thetheos/StrainGauge/photos/IMG_20170623_125859.jpg

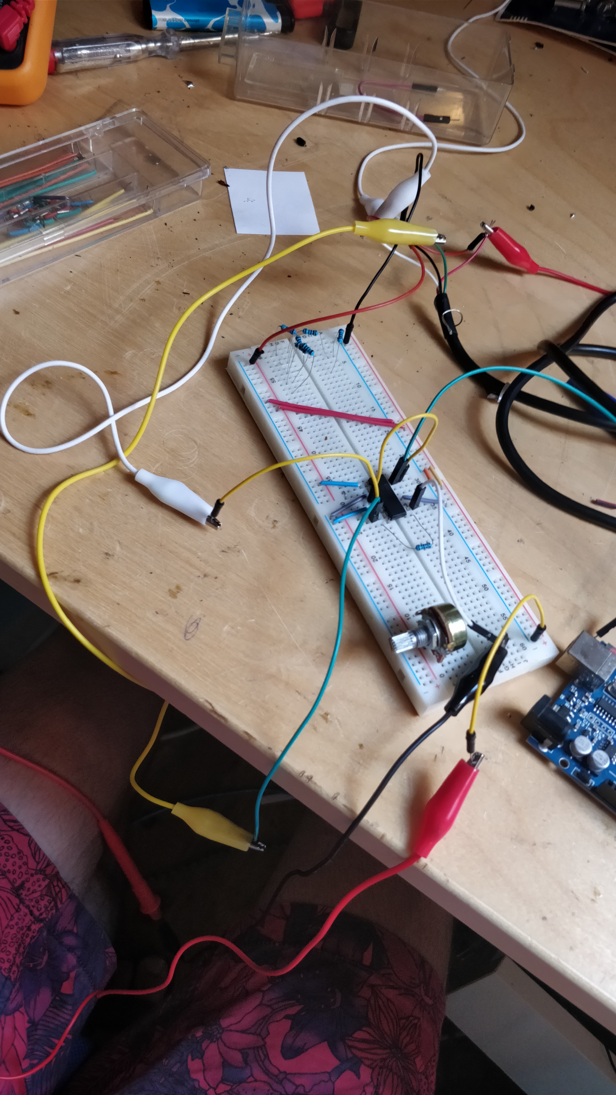
photos/IMG_20170623_125859.jpg
