thetheos/StrainGauge/photos/IMG_20170623_130728.jpg

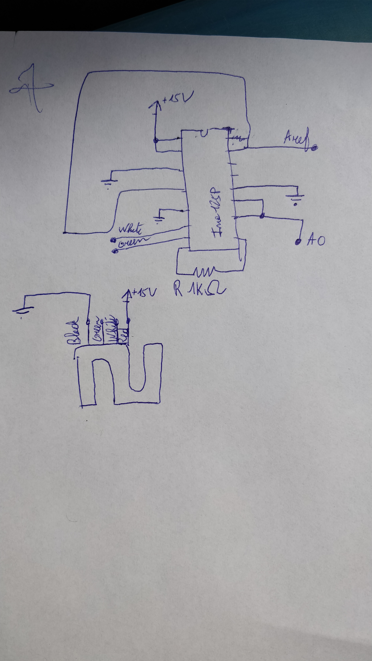
photos/IMG_20170623_130728.jpg
