thetheos/StrainGauge/photos/IMG_20170704_001040.jpg

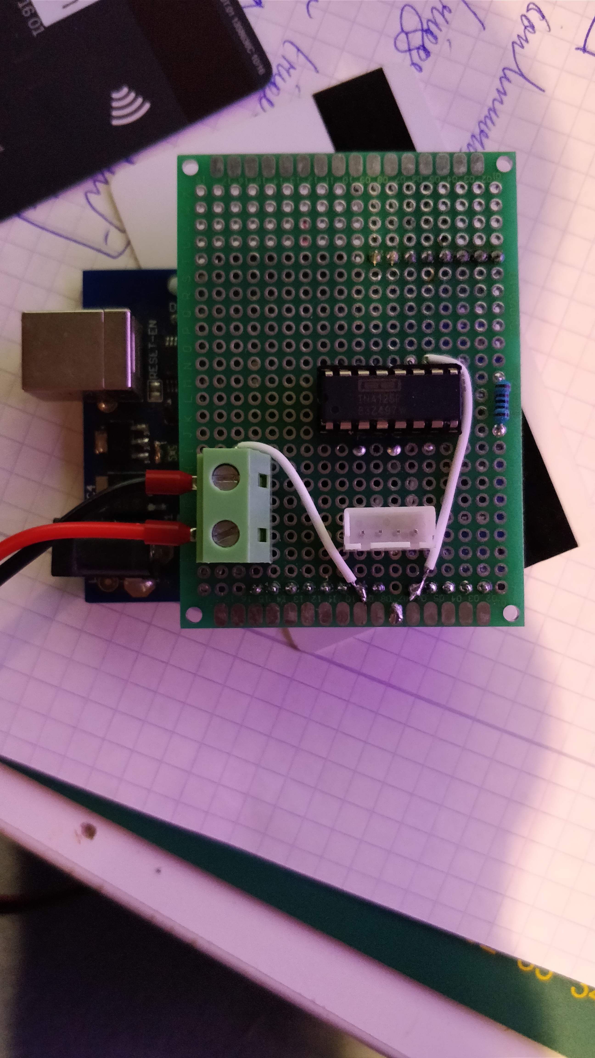
photos/IMG_20170704_001040.jpg
