thetheos/StrainGauge/test python/encoder.h

/* Encoder Library, for measuring quadrature encoded signals
 * http://www.pjrc.com/teensy/td_libs_Encoder.html
 * Copyright (c) 2011,2013 PJRC.COM, LLC - Paul Stoffregen <paul@pjrc.com>
 *
 * Version 1.2 - fix -2 bug in C-only code
 * Version 1.1 - expand to support boards with up to 60 interrupts
 * Version 1.0 - initial release
 * 
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
 * THE SOFTWARE IS PROVIDED "AS IS", WITHOUT WARRANTY OF ANY KIND, EXPRESS OR
 * IMPLIED, INCLUDING BUT NOT LIMITED TO THE WARRANTIES OF MERCHANTABILITY,
 * FITNESS FOR A PARTICULAR PURPOSE AND NONINFRINGEMENT. IN NO EVENT SHALL THE
 * AUTHORS OR COPYRIGHT HOLDERS BE LIABLE FOR ANY CLAIM, DAMAGES OR OTHER
 * LIABILITY, WHETHER IN AN ACTION OF CONTRACT, TORT OR OTHERWISE, ARISING FROM,
 * OUT OF OR IN CONNECTION WITH THE SOFTWARE OR THE USE OR OTHER DEALINGS IN
 * THE SOFTWARE.
 */


#ifndef Encoder_h_
#define Encoder_h_

#if defined(ARDUINO) && ARDUINO >= 100
#include "Arduino.h"
#elif defined(WIRING)
#include "Wiring.h"
#else
#include "WProgram.h"
#include "pins_arduino.h"
#endif

#include "utility/direct_pin_read.h"

#if defined(ENCODER_USE_INTERRUPTS) || !defined(ENCODER_DO_NOT_USE_INTERRUPTS)
#define ENCODER_USE_INTERRUPTS
#define ENCODER_ARGLIST_SIZE CORE_NUM_INTERRUPT
#include "utility/interrupt_pins.h"
#ifdef ENCODER_OPTIMIZE_INTERRUPTS
#include "utility/interrupt_config.h"
#endif
#else
#define ENCODER_ARGLIST_SIZE 0
#endif



// All the data needed by interrupts is consolidated into this ugly struct
// to facilitate assembly language optimizing of the speed critical update.
// The assembly code uses auto-incrementing addressing modes, so the struct
// must remain in exactly this order.
typedef struct {
	volatile IO_REG_TYPE * pin1_register;
	volatile IO_REG_TYPE * pin2_register;
	IO_REG_TYPE            pin1_bitmask;
	IO_REG_TYPE            pin2_bitmask;
	uint8_t                state;
	int32_t                position;
} Encoder_internal_state_t;

class Encoder
{
public:
	Encoder(uint8_t pin1, uint8_t pin2) {
		#ifdef INPUT_PULLUP
		pinMode(pin1, INPUT_PULLUP);
		pinMode(pin2, INPUT_PULLUP);
		#else
		pinMode(pin1, INPUT);
		digitalWrite(pin1, HIGH);
		pinMode(pin2, INPUT);
		digitalWrite(pin2, HIGH);
		#endif
		encoder.pin1_register = PIN_TO_BASEREG(pin1);
		encoder.pin1_bitmask = PIN_TO_BITMASK(pin1);
		encoder.pin2_register = PIN_TO_BASEREG(pin2);
		encoder.pin2_bitmask = PIN_TO_BITMASK(pin2);
		encoder.position = 0;
		// allow time for a passive R-C filter to charge
		// through the pullup resistors, before reading
		// the initial state
		delayMicroseconds(2000);
		uint8_t s = 0;
		if (DIRECT_PIN_READ(encoder.pin1_register, encoder.pin1_bitmask)) s |= 1;
		if (DIRECT_PIN_READ(encoder.pin2_register, encoder.pin2_bitmask)) s |= 2;
		encoder.state = s;
#ifdef ENCODER_USE_INTERRUPTS
		interrupts_in_use = attach_interrupt(pin1, &encoder);
		interrupts_in_use += attach_interrupt(pin2, &encoder);
#endif
		//update_finishup();  // to force linker to include the code (does not work)
	}


#ifdef ENCODER_USE_INTERRUPTS
	inline int32_t read() {
		if (interrupts_in_use < 2) {
			noInterrupts();
			update(&encoder);
		} else {
			noInterrupts();
		}
		int32_t ret = encoder.position;
		interrupts();
		return ret;
	}
	inline void write(int32_t p) {
		noInterrupts();
		encoder.position = p;
		interrupts();
	}
#else
	inline int32_t read() {
		update(&encoder);
		return encoder.position;
	}
	inline void write(int32_t p) {
		encoder.position = p;
	}
#endif
private:
	Encoder_internal_state_t encoder;
#ifdef ENCODER_USE_INTERRUPTS
	uint8_t interrupts_in_use;
#endif
public:
	static Encoder_internal_state_t * interruptArgs[ENCODER_ARGLIST_SIZE];

//                           _______         _______       
//               Pin1 ______|       |_______|       |______ Pin1
// negative <---         _______         _______         __      --> positive
//               Pin2 __|       |_______|       |_______|   Pin2

		//	new	new	old	old
		//	pin2	pin1	pin2	pin1	Result
		//	----	----	----	----	------
		//	0	0	0	0	no movement
		//	0	0	0	1	+1
		//	0	0	1	0	-1
		//	0	0	1	1	+2  (assume pin1 edges only)
		//	0	1	0	0	-1
		//	0	1	0	1	no movement
		//	0	1	1	0	-2  (assume pin1 edges only)
		//	0	1	1	1	+1
		//	1	0	0	0	+1
		//	1	0	0	1	-2  (assume pin1 edges only)
		//	1	0	1	0	no movement
		//	1	0	1	1	-1
		//	1	1	0	0	+2  (assume pin1 edges only)
		//	1	1	0	1	-1
		//	1	1	1	0	+1
		//	1	1	1	1	no movement
/*
	// Simple, easy-to-read "documentation" version :-)
	//
	void update(void) {
		uint8_t s = state & 3;
		if (digitalRead(pin1)) s |= 4;
		if (digitalRead(pin2)) s |= 8;
		switch (s) {
			case 0: case 5: case 10: case 15:
				break;
			case 1: case 7: case 8: case 14:
				position++; break;
			case 2: case 4: case 11: case 13:
				position--; break;
			case 3: case 12:
				position += 2; break;
			default:
				position -= 2; break;
		}
		state = (s >> 2);
	}
*/

private:
	static void update(Encoder_internal_state_t *arg) {
#if defined(__AVR__)
		// The compiler believes this is just 1 line of code, so
		// it will inline this function into each interrupt
		// handler.  That's a tiny bit faster, but grows the code.
		// Especially when used with ENCODER_OPTIMIZE_INTERRUPTS,
		// the inline nature allows the ISR prologue and epilogue
		// to only save/restore necessary registers, for very nice
		// speed increase.
		asm volatile (
			"ld	r30, X+"		"\n\t"
			"ld	r31, X+"		"\n\t"
			"ld	r24, Z"			"\n\t"	// r24 = pin1 input
			"ld	r30, X+"		"\n\t"
			"ld	r31, X+"		"\n\t"
			"ld	r25, Z"			"\n\t"  // r25 = pin2 input
			"ld	r30, X+"		"\n\t"  // r30 = pin1 mask
			"ld	r31, X+"		"\n\t"	// r31 = pin2 mask
			"ld	r22, X"			"\n\t"	// r22 = state
			"andi	r22, 3"			"\n\t"
			"and	r24, r30"		"\n\t"
			"breq	L%=1"			"\n\t"	// if (pin1)
			"ori	r22, 4"			"\n\t"	//	state |= 4
		"L%=1:"	"and	r25, r31"		"\n\t"
			"breq	L%=2"			"\n\t"	// if (pin2)
			"ori	r22, 8"			"\n\t"	//	state |= 8
		"L%=2:" "ldi	r30, lo8(pm(L%=table))"	"\n\t"
			"ldi	r31, hi8(pm(L%=table))"	"\n\t"
			"add	r30, r22"		"\n\t"
			"adc	r31, __zero_reg__"	"\n\t"
			"asr	r22"			"\n\t"
			"asr	r22"			"\n\t"
			"st	X+, r22"		"\n\t"  // store new state
			"ld	r22, X+"		"\n\t"
			"ld	r23, X+"		"\n\t"
			"ld	r24, X+"		"\n\t"
			"ld	r25, X+"		"\n\t"
			"ijmp"				"\n\t"	// jumps to update_finishup()
			// TODO move this table to another static function,
			// so it doesn't get needlessly duplicated.  Easier
			// said than done, due to linker issues and inlining
		"L%=table:"				"\n\t"
			"rjmp	L%=end"			"\n\t"	// 0
			"rjmp	L%=plus1"		"\n\t"	// 1
			"rjmp	L%=minus1"		"\n\t"	// 2
			"rjmp	L%=plus2"		"\n\t"	// 3
			"rjmp	L%=minus1"		"\n\t"	// 4
			"rjmp	L%=end"			"\n\t"	// 5
			"rjmp	L%=minus2"		"\n\t"	// 6
			"rjmp	L%=plus1"		"\n\t"	// 7
			"rjmp	L%=plus1"		"\n\t"	// 8
			"rjmp	L%=minus2"		"\n\t"	// 9
			"rjmp	L%=end"			"\n\t"	// 10
			"rjmp	L%=minus1"		"\n\t"	// 11
			"rjmp	L%=plus2"		"\n\t"	// 12
			"rjmp	L%=minus1"		"\n\t"	// 13
			"rjmp	L%=plus1"		"\n\t"	// 14
			"rjmp	L%=end"			"\n\t"	// 15
		"L%=minus2:"				"\n\t"
			"subi	r22, 2"			"\n\t"
			"sbci	r23, 0"			"\n\t"
			"sbci	r24, 0"			"\n\t"
			"sbci	r25, 0"			"\n\t"
			"rjmp	L%=store"		"\n\t"
		"L%=minus1:"				"\n\t"
			"subi	r22, 1"			"\n\t"
			"sbci	r23, 0"			"\n\t"
			"sbci	r24, 0"			"\n\t"
			"sbci	r25, 0"			"\n\t"
			"rjmp	L%=store"		"\n\t"
		"L%=plus2:"				"\n\t"
			"subi	r22, 254"		"\n\t"
			"rjmp	L%=z"			"\n\t"
		"L%=plus1:"				"\n\t"
			"subi	r22, 255"		"\n\t"
		"L%=z:"	"sbci	r23, 255"		"\n\t"
			"sbci	r24, 255"		"\n\t"
			"sbci	r25, 255"		"\n\t"
		"L%=store:"				"\n\t"
			"st	-X, r25"		"\n\t"
			"st	-X, r24"		"\n\t"
			"st	-X, r23"		"\n\t"
			"st	-X, r22"		"\n\t"
		"L%=end:"				"\n"
		: : "x" (arg) : "r22", "r23", "r24", "r25", "r30", "r31");
#else
		uint8_t p1val = DIRECT_PIN_READ(arg->pin1_register, arg->pin1_bitmask);
		uint8_t p2val = DIRECT_PIN_READ(arg->pin2_register, arg->pin2_bitmask);
		uint8_t state = arg->state & 3;
		if (p1val) state |= 4;
		if (p2val) state |= 8;
		arg->state = (state >> 2);
		switch (state) {
			case 1: case 7: case 8: case 14:
				arg->position++;
				return;
			case 2: case 4: case 11: case 13:
				arg->position--;
				return;
			case 3: case 12:
				arg->position += 2;
				return;
			case 6: case 9:
				arg->position -= 2;
				return;
		}
#endif
	}
/*
#if defined(__AVR__)
	// TODO: this must be a no inline function
	// even noinline does not seem to solve difficult
	// problems with this.  Oh well, it was only meant
	// to shrink code size - there's no performance
	// improvement in this, only code size reduction.
	__attribute__((noinline)) void update_finishup(void) {
		asm volatile (
			"ldi	r30, lo8(pm(Ltable))"	"\n\t"
			"ldi	r31, hi8(pm(Ltable))"	"\n\t"
		"Ltable:"				"\n\t"
			"rjmp	L%=end"			"\n\t"	// 0
			"rjmp	L%=plus1"		"\n\t"	// 1
			"rjmp	L%=minus1"		"\n\t"	// 2
			"rjmp	L%=plus2"		"\n\t"	// 3
			"rjmp	L%=minus1"		"\n\t"	// 4
			"rjmp	L%=end"			"\n\t"	// 5
			"rjmp	L%=minus2"		"\n\t"	// 6
			"rjmp	L%=plus1"		"\n\t"	// 7
			"rjmp	L%=plus1"		"\n\t"	// 8
			"rjmp	L%=minus2"		"\n\t"	// 9
			"rjmp	L%=end"			"\n\t"	// 10
			"rjmp	L%=minus1"		"\n\t"	// 11
			"rjmp	L%=plus2"		"\n\t"	// 12
			"rjmp	L%=minus1"		"\n\t"	// 13
			"rjmp	L%=plus1"		"\n\t"	// 14
			"rjmp	L%=end"			"\n\t"	// 15
		"L%=minus2:"				"\n\t"
			"subi	r22, 2"			"\n\t"
			"sbci	r23, 0"			"\n\t"
			"sbci	r24, 0"			"\n\t"
			"sbci	r25, 0"			"\n\t"
			"rjmp	L%=store"		"\n\t"
		"L%=minus1:"				"\n\t"
			"subi	r22, 1"			"\n\t"
			"sbci	r23, 0"			"\n\t"
			"sbci	r24, 0"			"\n\t"
			"sbci	r25, 0"			"\n\t"
			"rjmp	L%=store"		"\n\t"
		"L%=plus2:"				"\n\t"
			"subi	r22, 254"		"\n\t"
			"rjmp	L%=z"			"\n\t"
		"L%=plus1:"				"\n\t"
			"subi	r22, 255"		"\n\t"
		"L%=z:"	"sbci	r23, 255"		"\n\t"
			"sbci	r24, 255"		"\n\t"
			"sbci	r25, 255"		"\n\t"
		"L%=store:"				"\n\t"
			"st	-X, r25"		"\n\t"
			"st	-X, r24"		"\n\t"
			"st	-X, r23"		"\n\t"
			"st	-X, r22"		"\n\t"
		"L%=end:"				"\n"
		: : : "r22", "r23", "r24", "r25", "r30", "r31");
	}
#endif
*/


#ifdef ENCODER_USE_INTERRUPTS
	// this giant function is an unfortunate consequence of Arduino's
	// attachInterrupt function not supporting any way to pass a pointer
	// or other context to the attached function.
	static uint8_t attach_interrupt(uint8_t pin, Encoder_internal_state_t *state) {
		switch (pin) {
		#ifdef CORE_INT0_PIN
			case CORE_INT0_PIN:
				interruptArgs[0] = state;
				attachInterrupt(0, isr0, CHANGE);
				break;
		#endif
		#ifdef CORE_INT1_PIN
			case CORE_INT1_PIN:
				interruptArgs[1] = state;
				attachInterrupt(1, isr1, CHANGE);
				break;
		#endif
		#ifdef CORE_INT2_PIN
			case CORE_INT2_PIN:
				interruptArgs[2] = state;
				attachInterrupt(2, isr2, CHANGE);
				break;
		#endif
		#ifdef CORE_INT3_PIN
			case CORE_INT3_PIN:
				interruptArgs[3] = state;
				attachInterrupt(3, isr3, CHANGE);
				break;
		#endif
		#ifdef CORE_INT4_PIN
			case CORE_INT4_PIN:
				interruptArgs[4] = state;
				attachInterrupt(4, isr4, CHANGE);
				break;
		#endif
		#ifdef CORE_INT5_PIN
			case CORE_INT5_PIN:
				interruptArgs[5] = state;
				attachInterrupt(5, isr5, CHANGE);
				break;
		#endif
		#ifdef CORE_INT6_PIN
			case CORE_INT6_PIN:
				interruptArgs[6] = state;
				attachInterrupt(6, isr6, CHANGE);
				break;
		#endif
		#ifdef CORE_INT7_PIN
			case CORE_INT7_PIN:
				interruptArgs[7] = state;
				attachInterrupt(7, isr7, CHANGE);
				break;
		#endif
		#ifdef CORE_INT8_PIN
			case CORE_INT8_PIN:
				interruptArgs[8] = state;
				attachInterrupt(8, isr8, CHANGE);
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
	#endif
	#ifdef CORE_INT57_PIN
	static void isr57(void) { update(interruptArgs[57]); }
	#endif
	#ifdef CORE_INT58_PIN
	static void isr58(void) { update(interruptArgs[58]); }
	#endif
	#ifdef CORE_INT59_PIN
	static void isr59(void) { update(interruptArgs[59]); }
	#endif
#endif
};

#if defined(ENCODER_USE_INTERRUPTS) && defined(ENCODER_OPTIMIZE_INTERRUPTS)
#if defined(__AVR__)
#if defined(INT0_vect) && CORE_NUM_INTERRUPT > 0
ISR(INT0_vect) { Encoder::update(Encoder::interruptArgs[SCRAMBLE_INT_ORDER(0)]); }
#endif
#if defined(INT1_vect) && CORE_NUM_INTERRUPT > 1
ISR(INT1_vect) { Encoder::update(Encoder::interruptArgs[SCRAMBLE_INT_ORDER(1)]); }
#endif
#if defined(INT2_vect) && CORE_NUM_INTERRUPT > 2
ISR(INT2_vect) { Encoder::update(Encoder::interruptArgs[SCRAMBLE_INT_ORDER(2)]); }
#endif
#if defined(INT3_vect) && CORE_NUM_INTERRUPT > 3
ISR(INT3_vect) { Encoder::update(Encoder::interruptArgs[SCRAMBLE_INT_ORDER(3)]); }
#endif
#if defined(INT4_vect) && CORE_NUM_INTERRUPT > 4
ISR(INT4_vect) { Encoder::update(Encoder::interruptArgs[SCRAMBLE_INT_ORDER(4)]); }
#endif
#if defined(INT5_vect) && CORE_NUM_INTERRUPT > 5
ISR(INT5_vect) { Encoder::update(Encoder::interruptArgs[SCRAMBLE_INT_ORDER(5)]); }
#endif
#if defined(INT6_vect) && CORE_NUM_INTERRUPT > 6
ISR(INT6_vect) { Encoder::update(Encoder::interruptArgs[SCRAMBLE_INT_ORDER(6)]); }
#endif
#if defined(INT7_vect) && CORE_NUM_INTERRUPT > 7
ISR(INT7_vect) { Encoder::update(Encoder::interruptArgs[SCRAMBLE_INT_ORDER(7)]); }
#endif
#endif // AVR
#endif // ENCODER_OPTIMIZE_INTERRUPTS


#endif
